DIYSynthMNL/Eurorack-Multi-Saturation-Module/photos/board.jpg

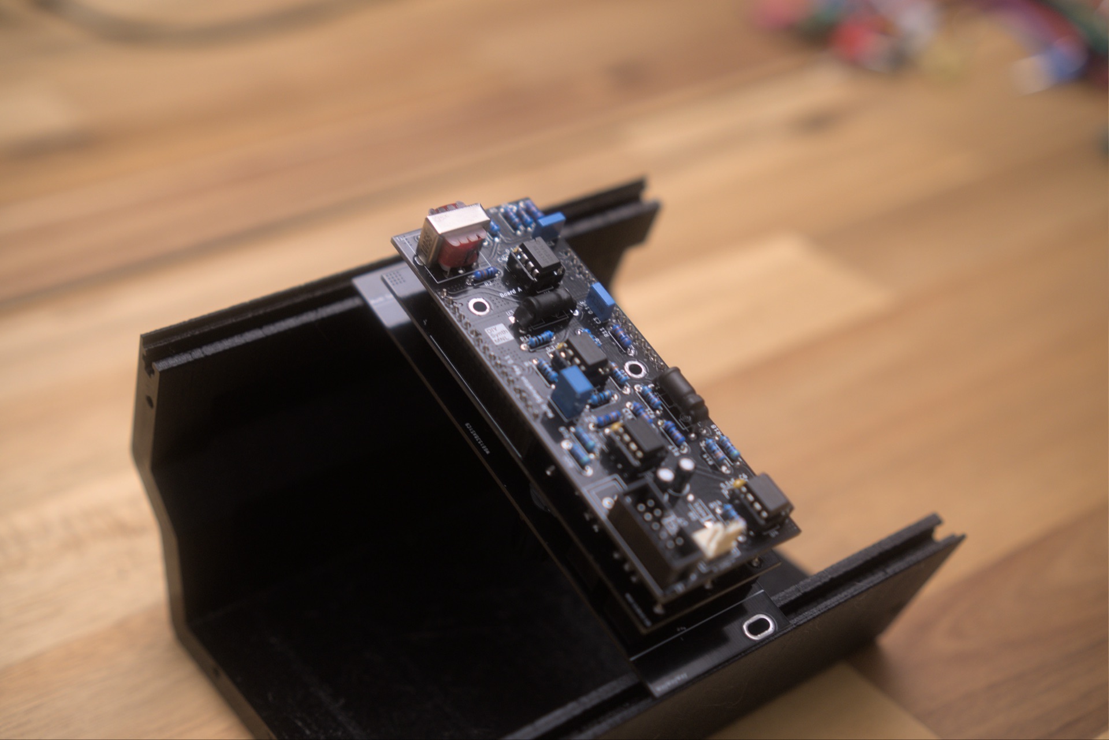
photos/board.jpg
