DIYSynthMNL/Eurorack-Multi-Saturation-Module/photos/front-flat.jpg

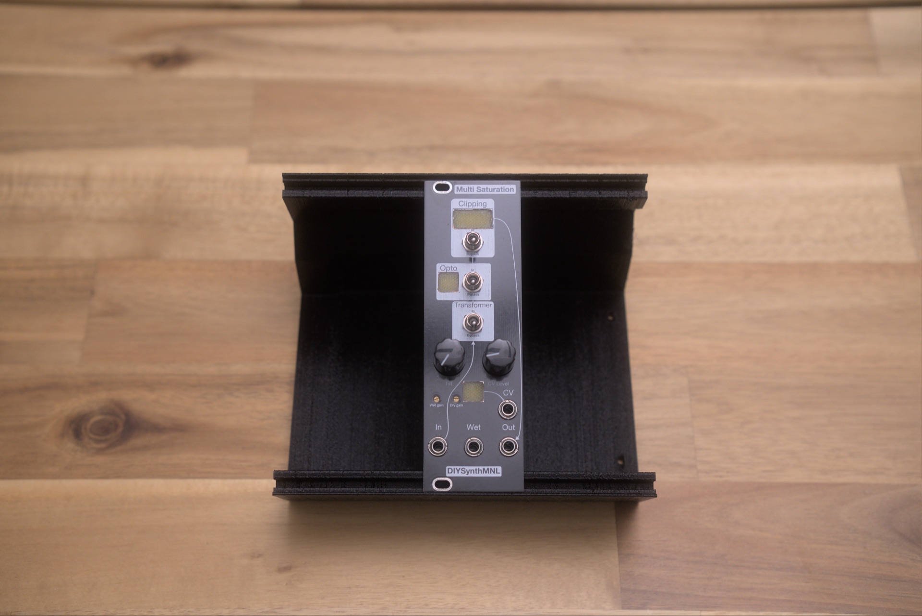
photos/front-flat.jpg
