DIYSynthMNL/Eurorack-Multi-Saturation-Module/photos/pcb-edge.jpg

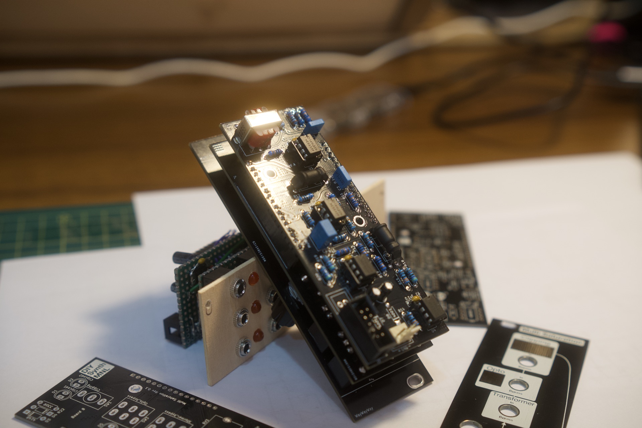
photos/pcb-edge.jpg
