DIYSynthMNL/Eurorack-Multi-Saturation-Module/photos/prototyping/proto-02.jpg

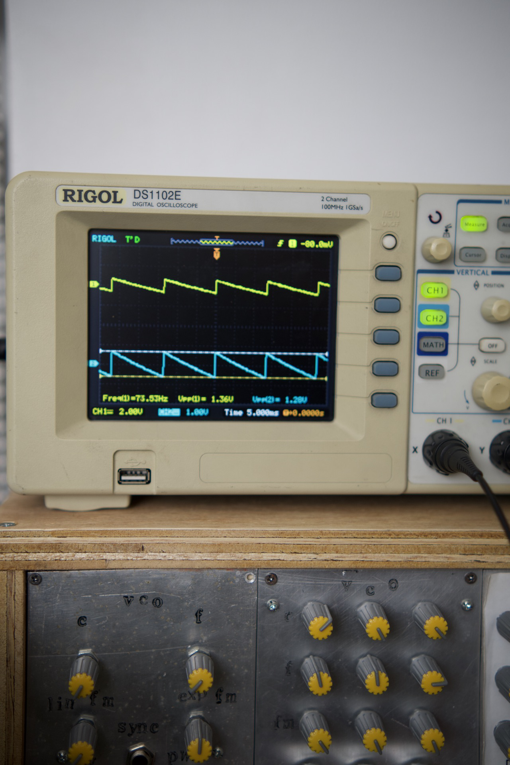
photos/prototyping/proto-02.jpg
