DIYSynthMNL/Eurorack-Multi-Saturation-Module/photos/prototyping/proto-03.jpg

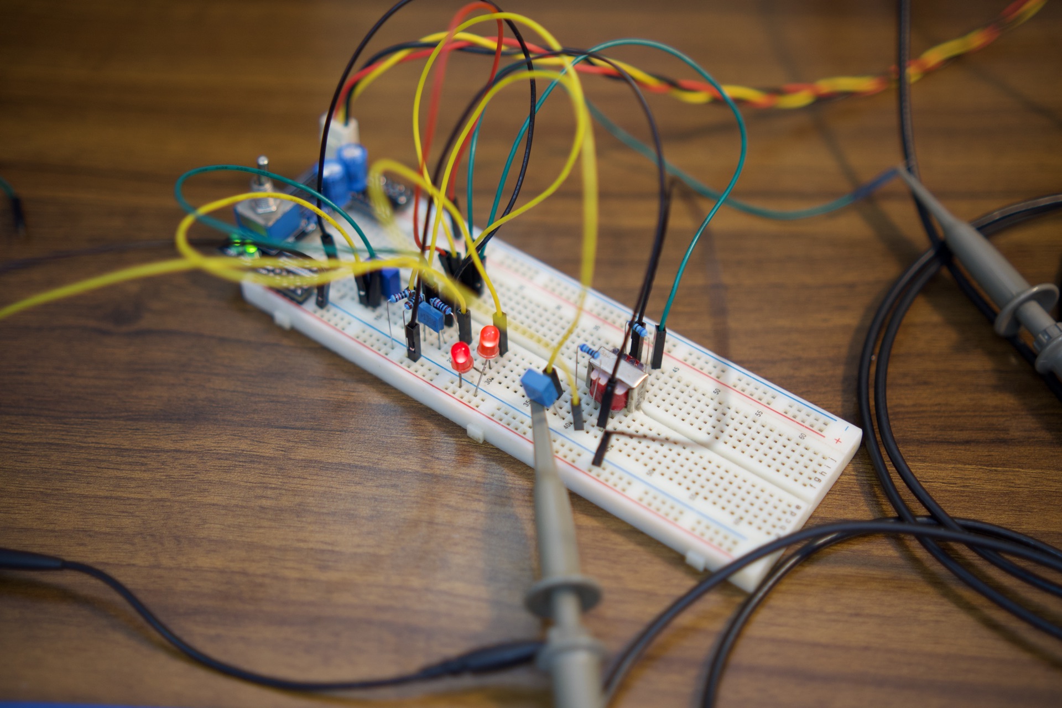
photos/prototyping/proto-03.jpg
