DIYSynthMNL/Eurorack-Multi-Saturation-Module/photos/prototyping/proto-04.jpg

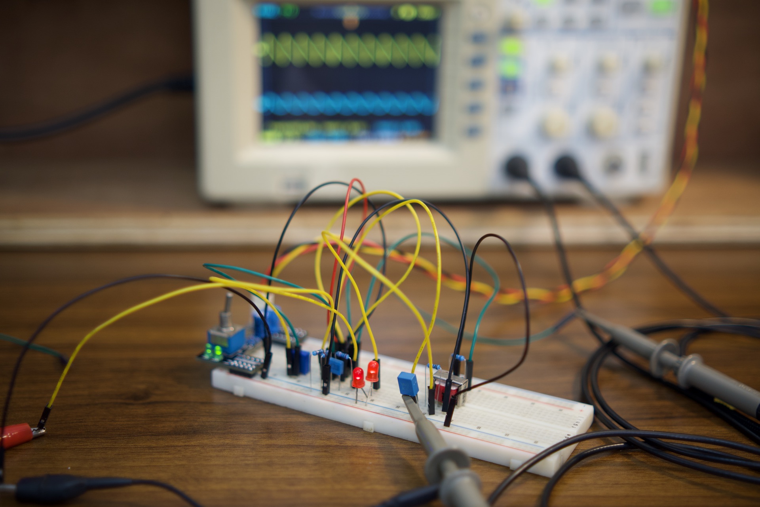
photos/prototyping/proto-04.jpg
