DIYSynthMNL/Eurorack-Multi-Saturation-Module/photos/prototyping/proto-05.jpg

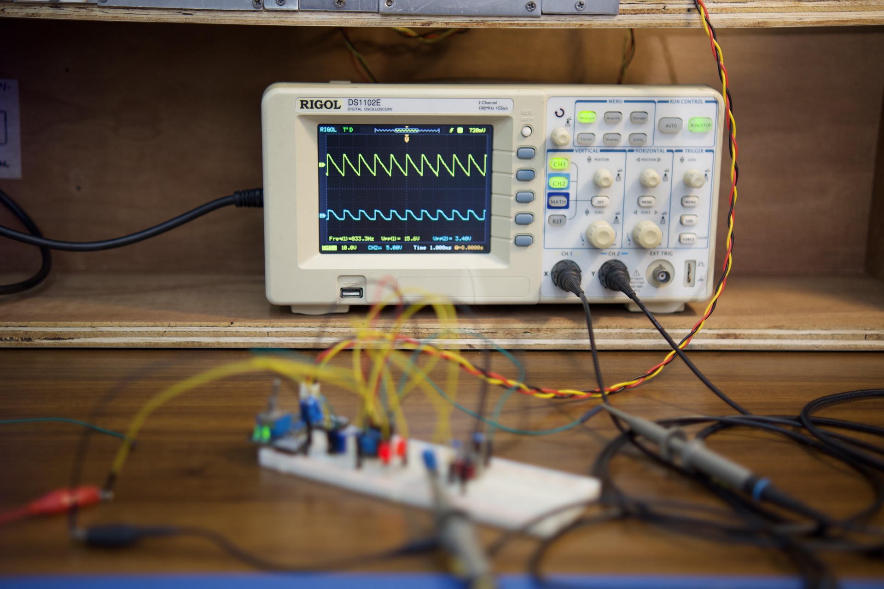
photos/prototyping/proto-05.jpg
