DIYSynthMNL/Eurorack-Multi-Saturation-Module/photos/prototyping/proto-06.jpg

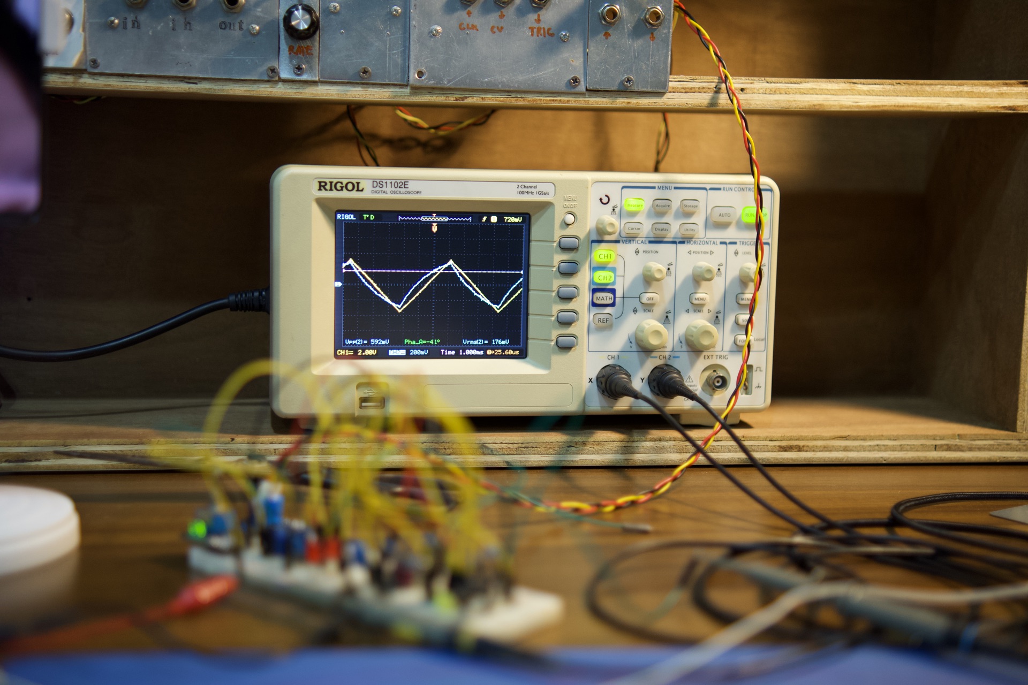
photos/prototyping/proto-06.jpg
