DIYSynthMNL/Eurorack-Multi-Saturation-Module/photos/prototyping/proto-10.jpg

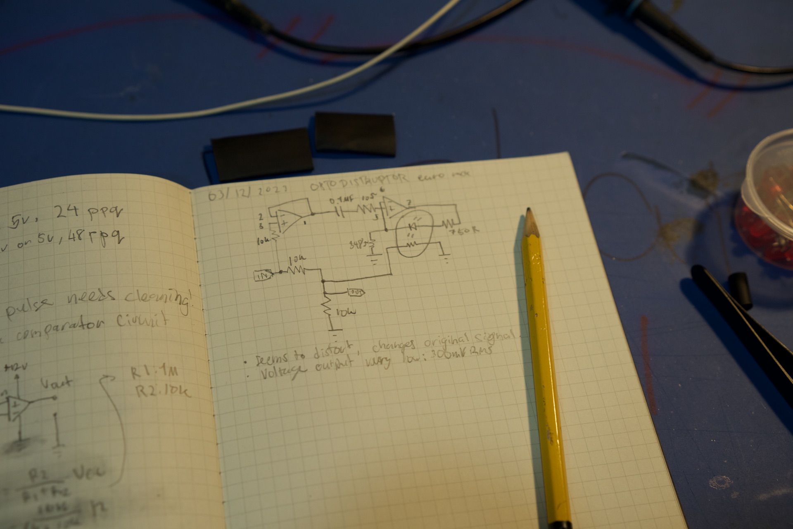
photos/prototyping/proto-10.jpg
