DIYSynthMNL/Eurorack-Multi-Saturation-Module/photos/prototyping/proto-11.jpg

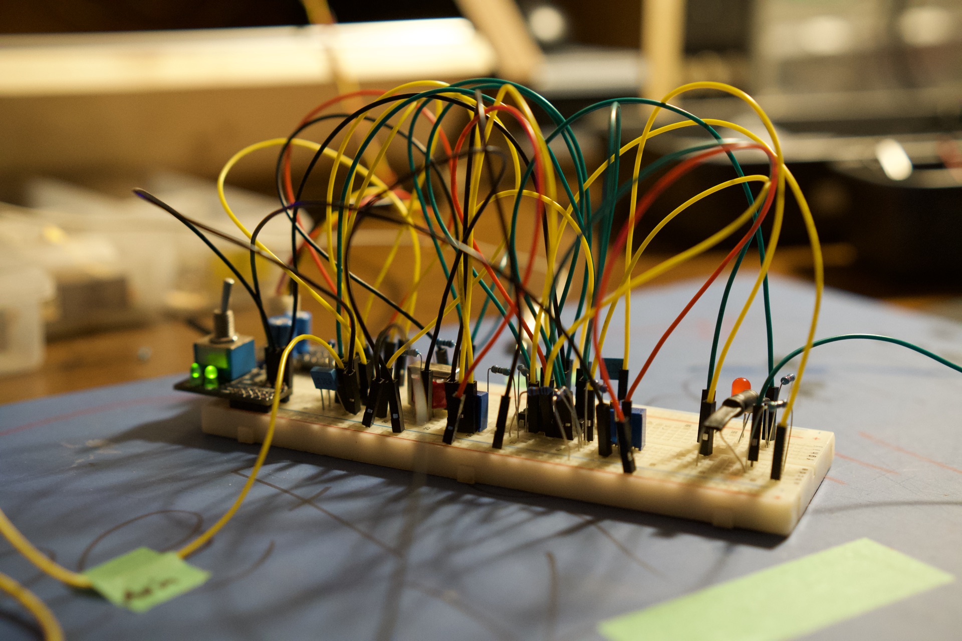
photos/prototyping/proto-11.jpg
