DIYSynthMNL/Eurorack-Multi-Saturation-Module/photos/prototyping/proto-13.jpg

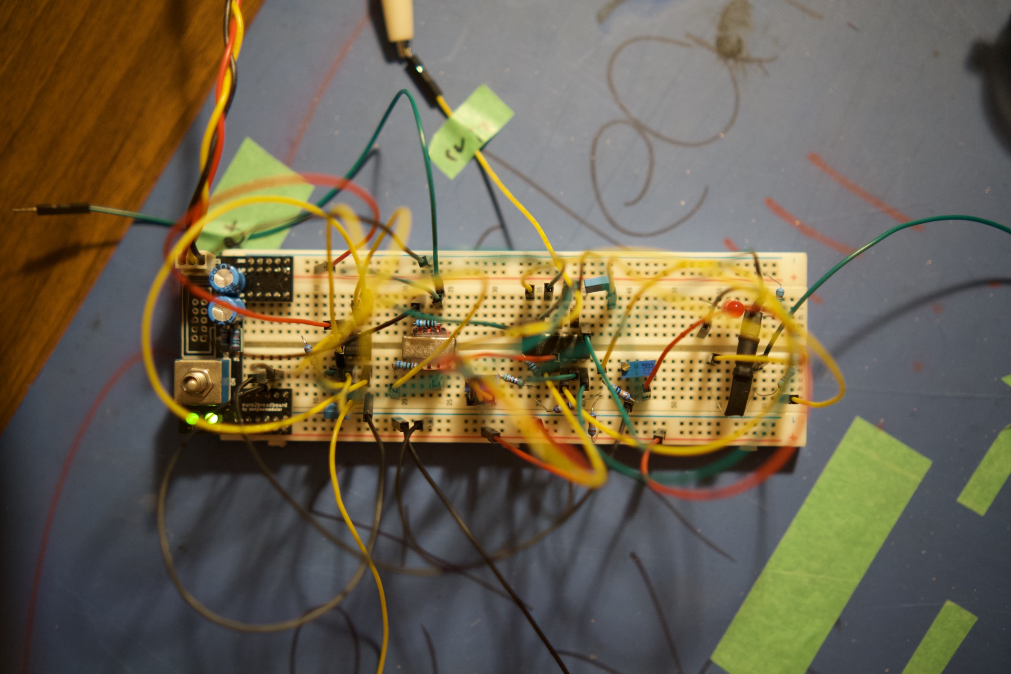
photos/prototyping/proto-13.jpg
