DIYSynthMNL/Eurorack-Multi-Saturation-Module/photos/prototyping/proto-14.jpg

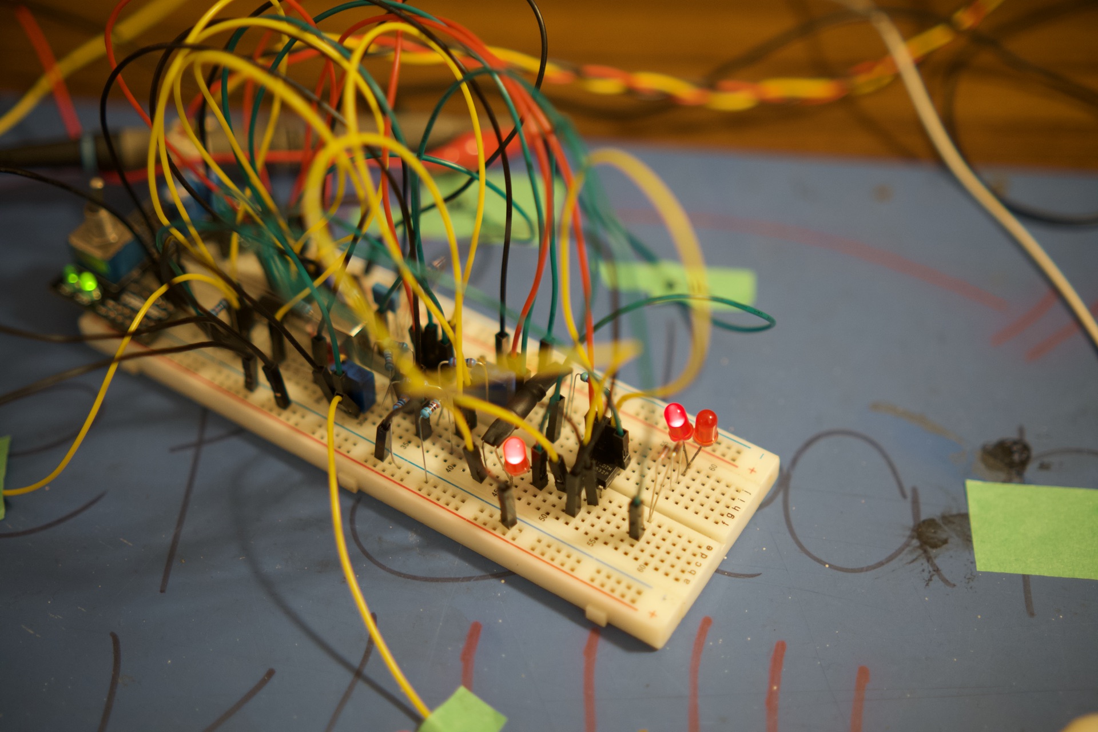
photos/prototyping/proto-14.jpg
