DIYSynthMNL/Eurorack-Multi-Saturation-Module/photos/assembly.jpg

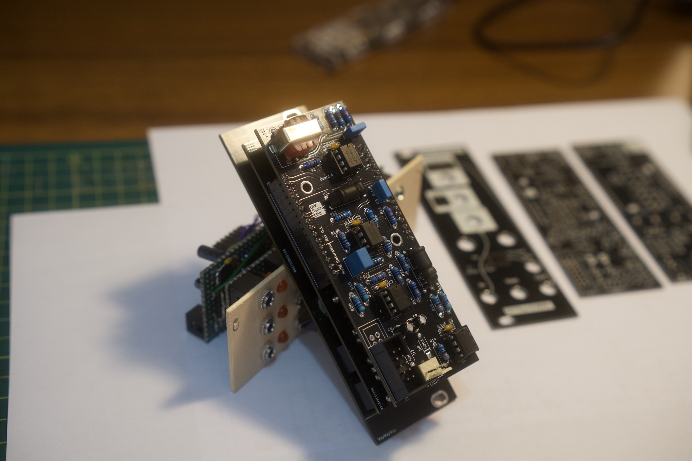
photos/assembly.jpg
